mlab-modules/VLFANT01/doc/gen/img/VLFANT01B-bottom.png

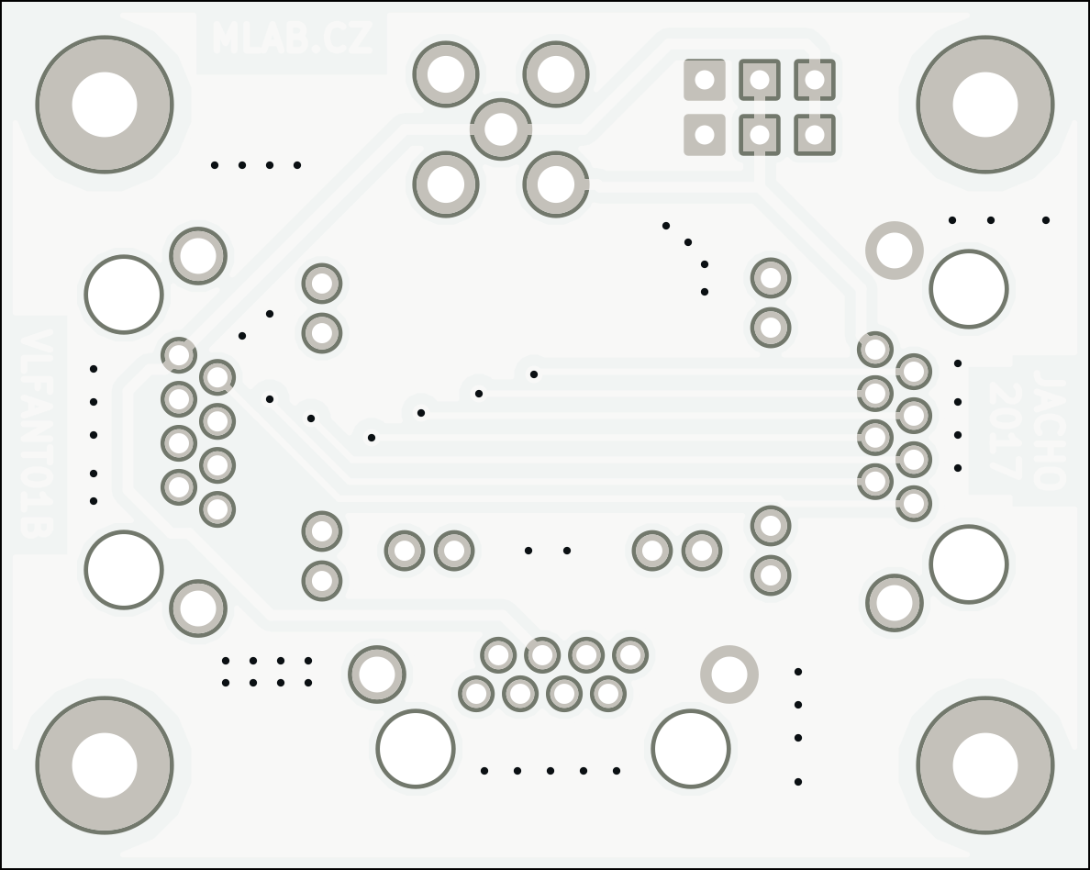
doc/gen/img/VLFANT01B-bottom.png
