mlab-modules/VLFANT01/doc/gen/img/VLFANT01B-top.png

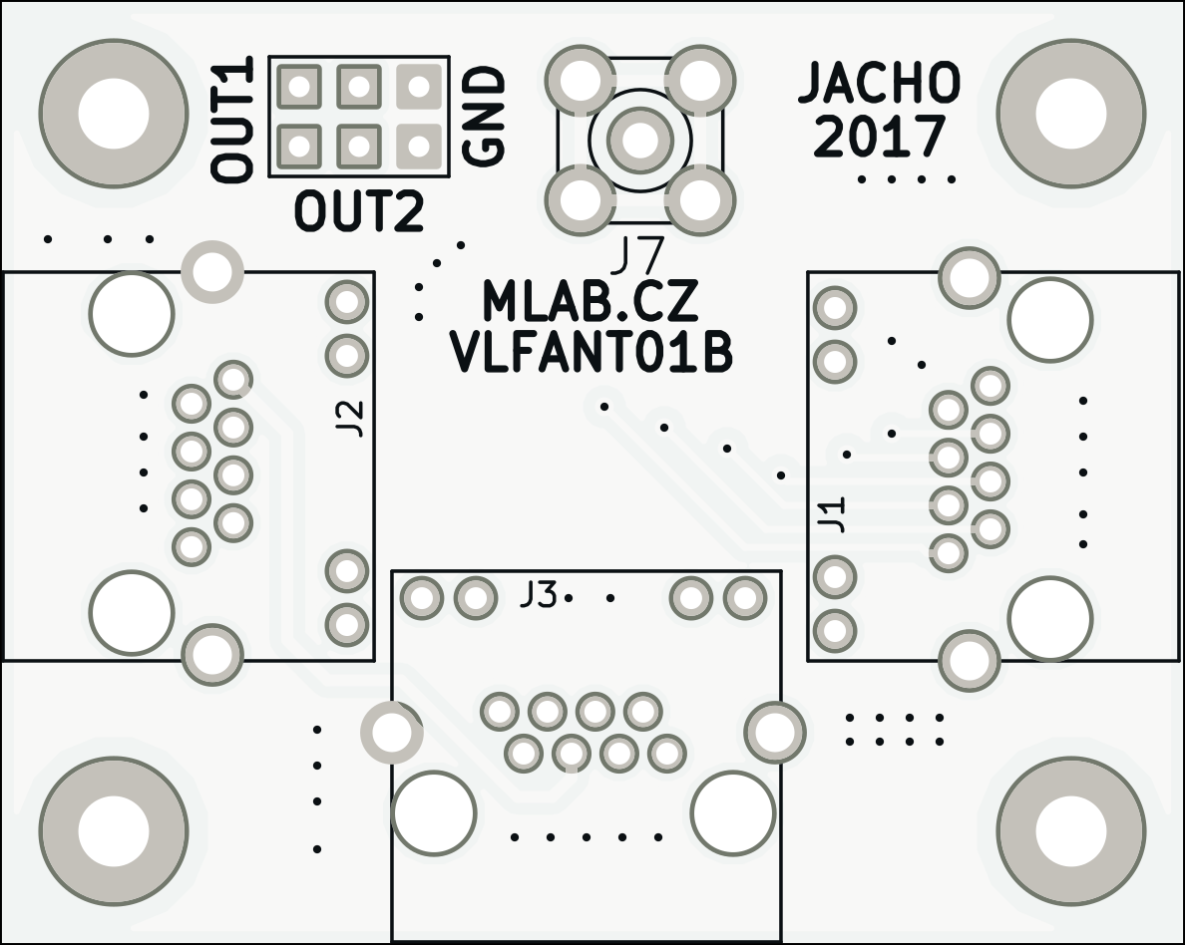
doc/gen/img/VLFANT01B-top.png
