mlab-modules/VLFANT01/doc/img/Antenna_construction/antenna_circle.jpg

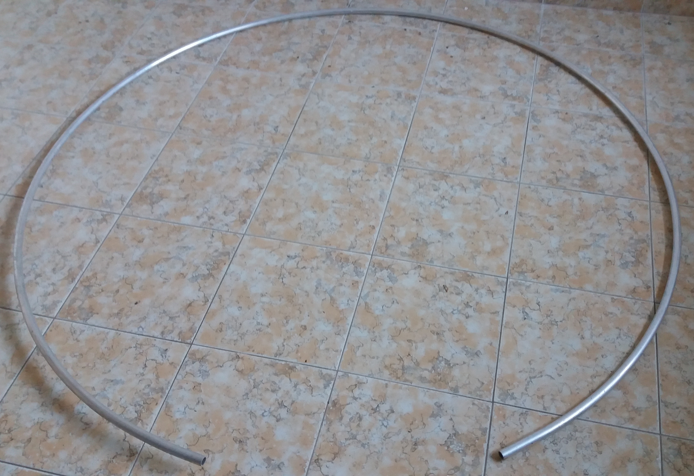
doc/img/Antenna_construction/antenna_circle.jpg
