mlab-modules/VLFANT01/doc/img/Antenna_construction/box_bushing_intalled.jpg

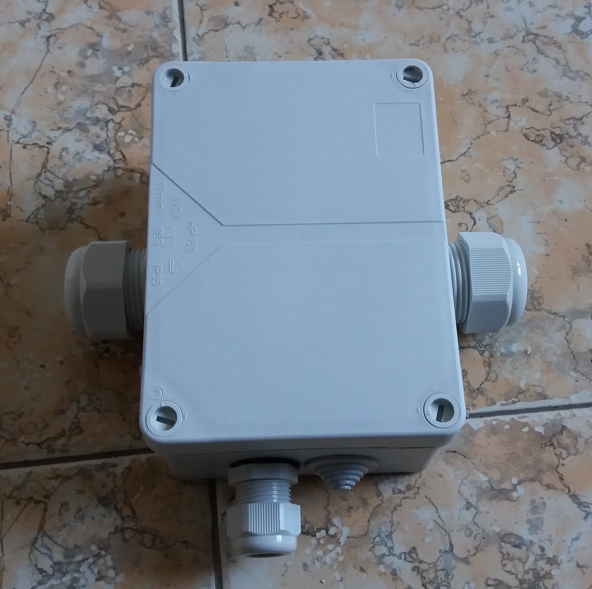
doc/img/Antenna_construction/box_bushing_intalled.jpg
