mlab-modules/VLFANT01/doc/img/Antenna_construction/box_cable_ends.jpg

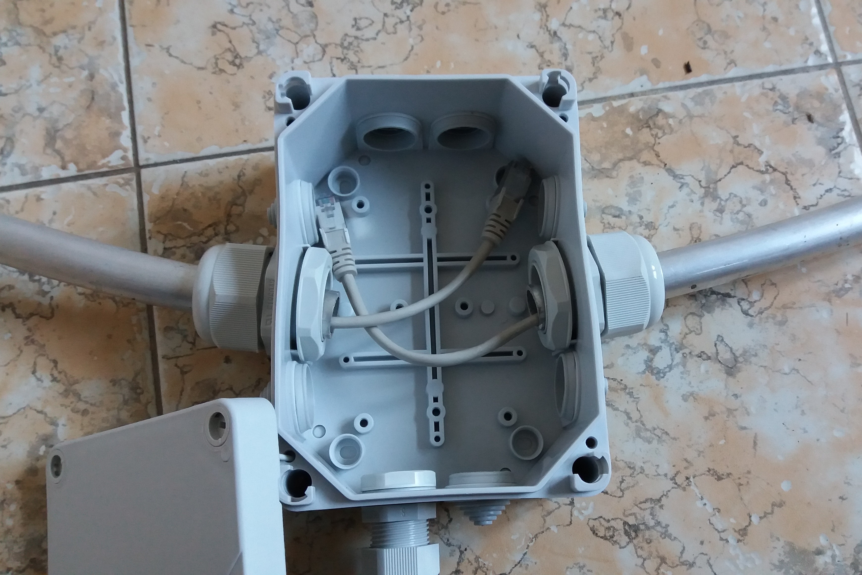
doc/img/Antenna_construction/box_cable_ends.jpg
