mlab-modules/VLFANT01/doc/img/Antenna_construction/mounting_strip3.jpg

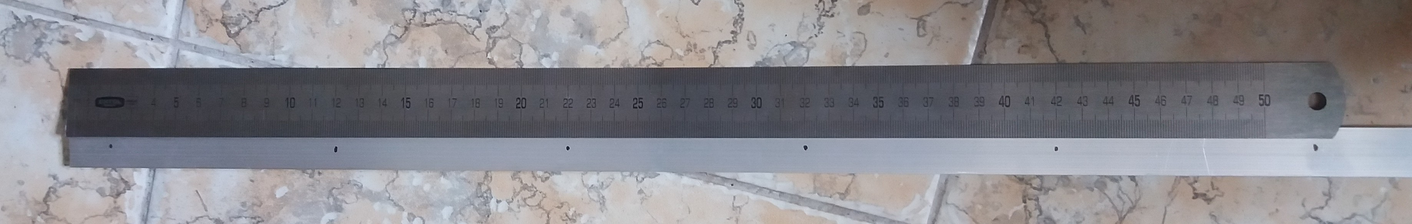
doc/img/Antenna_construction/mounting_strip3.jpg
