mlab-modules/VLFANT01/doc/img/Antenna_construction/UTP_insertion.jpg

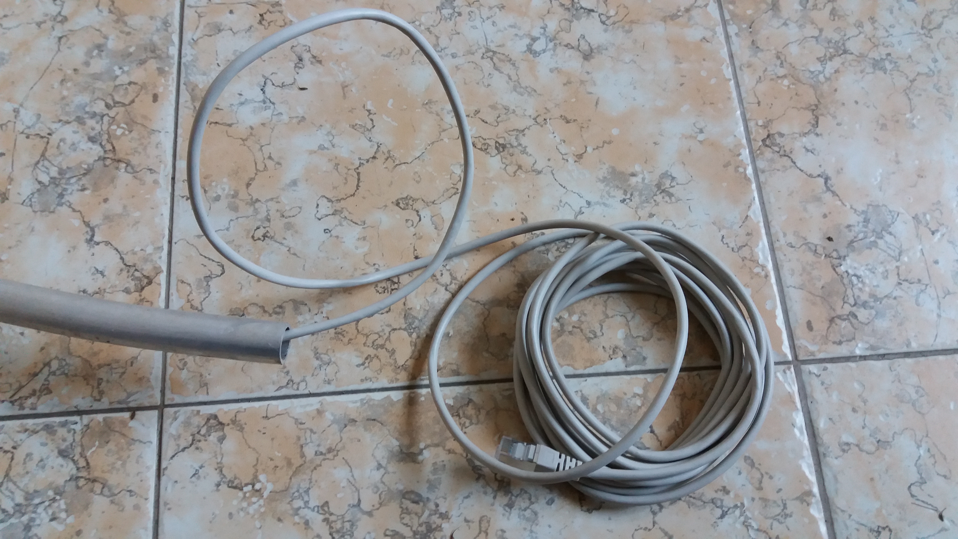
doc/img/Antenna_construction/UTP_insertion.jpg
